ill-ev-concept/EVC-PCB/images/Update_From_Main.png

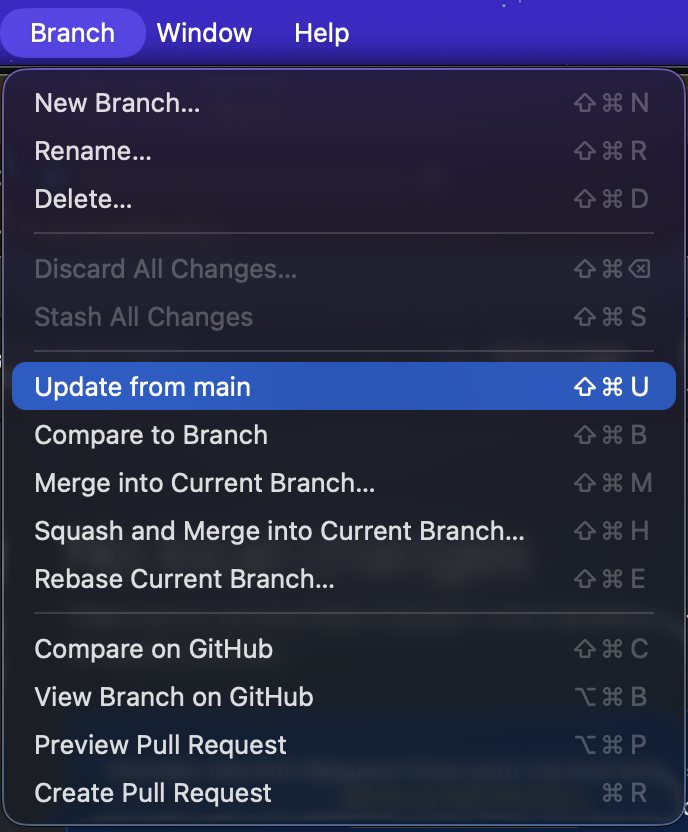
images/Update_From_Main.png
